svofski/vector06c-lesshadoks/6502/floppysrc/slave.c

// ====================================================================
//                         VECTOR-06C FPGA REPLICA
//
//               Copyright (C) 2007, 2008 Viacheslav Slavinsky
//
// This code is distributed under modified BSD license. 
// For complete licensing information see LICENSE.TXT.
// -------------------------------------------------------------------- 
//
// An open implementation of Vector-06C home computer
//
// Author: Viacheslav Slavinsky, http://sensi.org/~svo
// 
// Source file: slave.c
//
// Main request handler, runs eternally
//
// --------------------------------------------------------------------

#include <string.h>
#include "slave.h"
#include "specialio.h"
#include "tff.h"
#include "fddimage.h"
#include "integer.h"
#include "timer.h"
#include "menu.h"
#include "philes.h"
#include "diskio.h"
#include "serial.h"
#include "joy.h"


#define vputs(s) {}
#define vputc(s) {}
#define vputh(s) {}
#define vdump(s) {}
#define vnl()	 {}

#if VERBOSE >= 3
#undef vdump
#define vdump(b)  print_buff(b)
#endif

#if VERBOSE >= 2
#undef vputs
#undef vputc
#undef vputh
#undef vnl
#define vputs(s) ser_puts(s)
#define vputc(c) ser_putc(c)
#define vputh(x) print_hex(x)
#define vnl()	   ser_nl()
#endif

FDDImage fddimage;
FIL	file1;

#define DELAY_RELOAD 255 //128

uint8_t blink(void);
uint8_t loop_until_diskchange(void);

extern char * fdda;
extern char * fddb;
extern char * fdda_name;
extern char * fddb_name;

uint8_t thrall(uint8_t *buffer) 
{
    uint8_t first = 0;
    uint8_t result;

    SLAVE_STATUS = CPU_STATUS_DRVNOTRDY;

    for(;;) {
        SLAVE_STATUS = CPU_STATUS_DRVNOTRDY;
        do {
            result = philes_mount();
            ser_puts("mount() result=\n"); print_hex(result); ser_nl();
            result = philes_opendir(SUB_FDD);
            ser_puts("opendir() result=\n"); print_hex(result); ser_nl();
            if (result != FR_OK) break;

            ///* first run, initialise imagefile with the first file in the dir */
            //if (!first) {
            //    philes_nextfile(imagefile+10, 1);
            //    first++;
            //}

            ser_nl();
            if ((result = f_open(&file1, fdda, FA_READ)) != FR_OK) {
                ser_puts("Error opening: "); ser_puts(fdda); ser_nl();
                if (!first) {
                    philes_nextfile(fdda_name, 1);
                    ser_puts("Will try instead: "); ser_puts(fdda); ser_nl();
                    ++first;
                    continue;
                }
                first = 0; // try to recover by re-reading the directory
            } else {
                ser_puts("=> ");
            }
            ser_puts(fdda); ser_putc('$');ser_nl();

            if (result != FR_OK) break;

            fdd_load(&file1, &fddimage, buffer);
            loop_until_diskchange();
            /* slave exits when a new image file is selected */
        } while(0);
        menu_busy(2);
        menu_dispatch(0);
        delay2(10);
    }

    return 0;
}

// thrall forever
uint8_t loop_until_diskchange(void) 
{
    uint8_t result;
    uint8_t t1;
    uint8_t cmd;

    SLAVE_STATUS = 0;	// clear drive not ready flag

    for (;result != FR_RW_ERROR;) {
        //SLAVE_STATUS = 0;
        result = FR_OK;
        if (disk_poll(0) == RES_NOTRDY) {
            vputs("NOSD");
            break;
        }

        cmd = MASTER_COMMAND;
        switch (cmd & 0xf0) {
            case CPU_REQUEST_READ:
                SLAVE_STATUS = CPU_STATUS_BUSY;
                menu_busy(1);
                vnl();
                vputs("rHST:");
                t1 = cmd & 0x02; // side

                if (t1 == 0) {
                    fdd_seek(&fddimage, 0x01 & cmd, MASTER_TRACK, MASTER_SECTOR);

                    vputh(fddimage.cur_side);
                    vputh(fddimage.cur_sector);
                    vputh(fddimage.cur_track);

                    result = fdd_readsector(&fddimage);

                    vputc(':');
                    vputh(result);
                    vdump(fddimage.buffer);
                } else {
                    result = FR_INVALID_DRIVE;
                    vputs("DRVERR");
                }

                SLAVE_STATUS = CPU_STATUS_COMPLETE | 
                    (result == FR_OK ? CPU_STATUS_SUCCESS : 0) | 
                    (result == FR_RW_ERROR ? CPU_STATUS_CRC : 0);
                // touche!

                break;
            case CPU_REQUEST_READADDR:
                // fill the beginning of buffer with position info
                // 6 bytes: track, side, sector, sectorsize code, crc1, crc2
                SLAVE_STATUS = CPU_STATUS_BUSY;

                menu_busy(1);
                vnl();
                vputc('Q');
                t1 = cmd & 0x02; // side

                if (t1 == 0) {
                    fdd_seek(&fddimage, 0x01 & cmd, MASTER_TRACK, MASTER_SECTOR);
                    result = fdd_readadr(&fddimage);

                    //for (t1 = 0; t1 < 6; t1++) vputh(buffer[t1]);
                } else {
                    result = FR_INVALID_DRIVE;
                    vputs("DRVERR");
                }

                SLAVE_STATUS = CPU_STATUS_COMPLETE | 
                    (result == FR_OK ? CPU_STATUS_SUCCESS : 0);
                // touche!
                break;
            case CPU_REQUEST_WRITE:
                SLAVE_STATUS = CPU_STATUS_BUSY;
                menu_busy(1);
                vnl();
                vputh(cmd);
                vputh(MASTER_TRACK);
                vputs("wHST:");

                if (t1 == 0) {
                    fdd_seek(&fddimage, 0x01 & cmd, MASTER_TRACK, MASTER_SECTOR);

                    vputh(fddimage.cur_side);
                    vputh(fddimage.cur_sector);
                    vputh(fddimage.cur_track);
                    vputh(MASTER_TRACK);

                    result = fdd_writesector(&fddimage);

                    vputc(':');
                    vputh(result);
                    vdump(fddimage.buffer);
                } else {
                    result = FR_INVALID_DRIVE;
                    vputs("DRVERR");
                }

                SLAVE_STATUS = CPU_STATUS_COMPLETE | 
                    (result == FR_OK ? CPU_STATUS_SUCCESS : 0) | 
                    (result == FR_RW_ERROR ? CPU_STATUS_CRC : 0);
                break;
            case CPU_REQUEST_ACK:
                SLAVE_STATUS = 0;
                vputc('+'); vputh(cmd & 0x0f); // print boo code
                break;
            case CPU_REQUEST_NOP:
                SLAVE_STATUS = CPU_STATUS_BUSY;
                vputc('`');
                vputh(cmd);
                vputh(MASTER_SECTOR);
                vputh(MASTER_TRACK);
                SLAVE_STATUS = CPU_STATUS_COMPLETE;
                break;
            case CPU_REQUEST_FAIL:
                SLAVE_STATUS = 0;
                vputs("Death by snoo-snoo:");
                vputh(cmd);
                vputs("CMD:");
                vputh(MASTER_SECTOR);
                vputs(" STATE:");
                vputh(MASTER_TRACK);
                vnl();
                vputs("X_x");
                for(;;);
                break;
            default:
                SLAVE_STATUS = 0;
                if ((result = blink()) != MENURESULT_NOTHING) {
                    return result;
                }
                break;
        }
    }

    SLAVE_STATUS = 0;
    return result;
}

uint8_t blink(void) 
{
    static uint8_t leds = 0x01;
    static uint8_t delay = 1;
    static uint8_t tick;

    tick = --delay == 0;

    menu_busy(0);

    //GREEN_LEDS = JOYSTICK;
    if (tick) {
        delay = DELAY_RELOAD;
        GREEN_LEDS = leds;
        leds <<= 1;
        if (leds == 0) leds = 0x01;
    }

    joy_tick(tick);

    return menu_dispatch(tick);
}
